FKW9/esp-smartmeter-netznoe/config.h

// WiFi Hostname
#ifdef TEST_SETUP
    #define HOSTNAME "FakeSmartmeter"
#else
    #define HOSTNAME "Smartmeter"
#endif

// Comment out next line to disable SD Card logging
// Also disables the Fileserver
// #define SD_CARD_LOGGING

// If you get a new Smartmeter, the overall energy counter gets reset.
// Input your latest measurement here to add it to the new values.
// Unit = Wh
#define ACTIVE_ENERGY_PLUS_OFFSET 9520525

// Comment out next line to disable Graphite logging
#define USE_GRAPHITE

#ifdef USE_GRAPHITE
    #define GRAPHITE_HOST "192.168.8.42"    // IP and Port of your Graphite Host
    #define GRAPHITE_PORT 2003              // Port must be standard metric line receiver
#endif
